Andrew-Sherwin/ECE395/Digital Target System/PCB Art/Asuka Langley/Asuka Langley w White Background.png

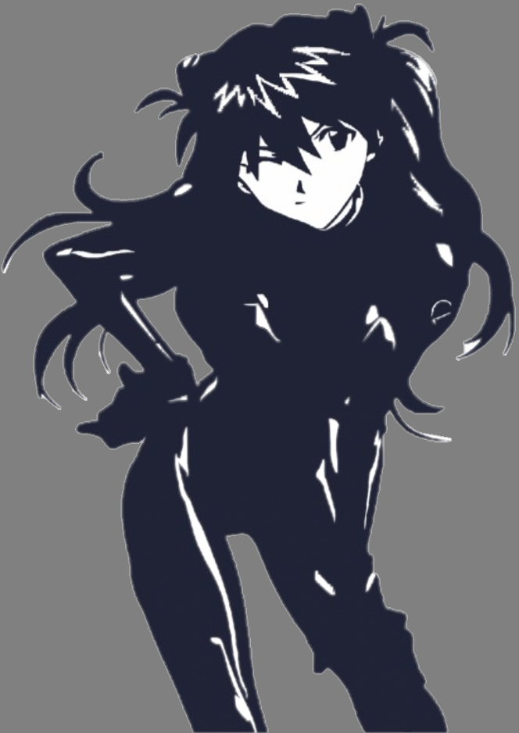
Digital Target System/PCB Art/Asuka Langley/Asuka Langley w White Background.png
