Andrew-Sherwin/ECE395/Digital Target System/PCB Art/Asuka Langley/Screen Shot 2023-11-08 at 3.01.39 AM.png

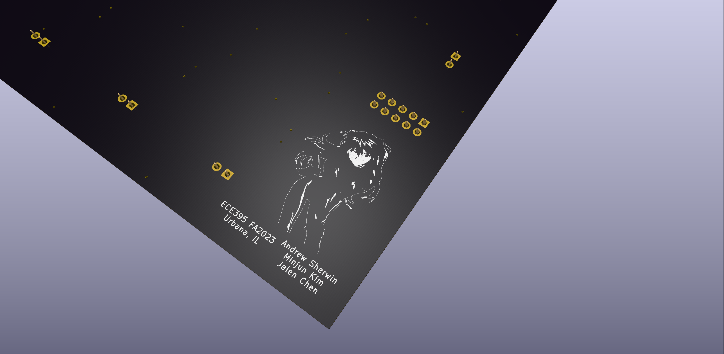
Digital Target System/PCB Art/Asuka Langley/Screen Shot 2023-11-08 at 3.01.39 AM.png
