Andrew-Sherwin/ECE395/Digital Target System/PCB Art/PSG Anime Girl/Screen Shot 2023-11-18 at 3.03.04 AM.png

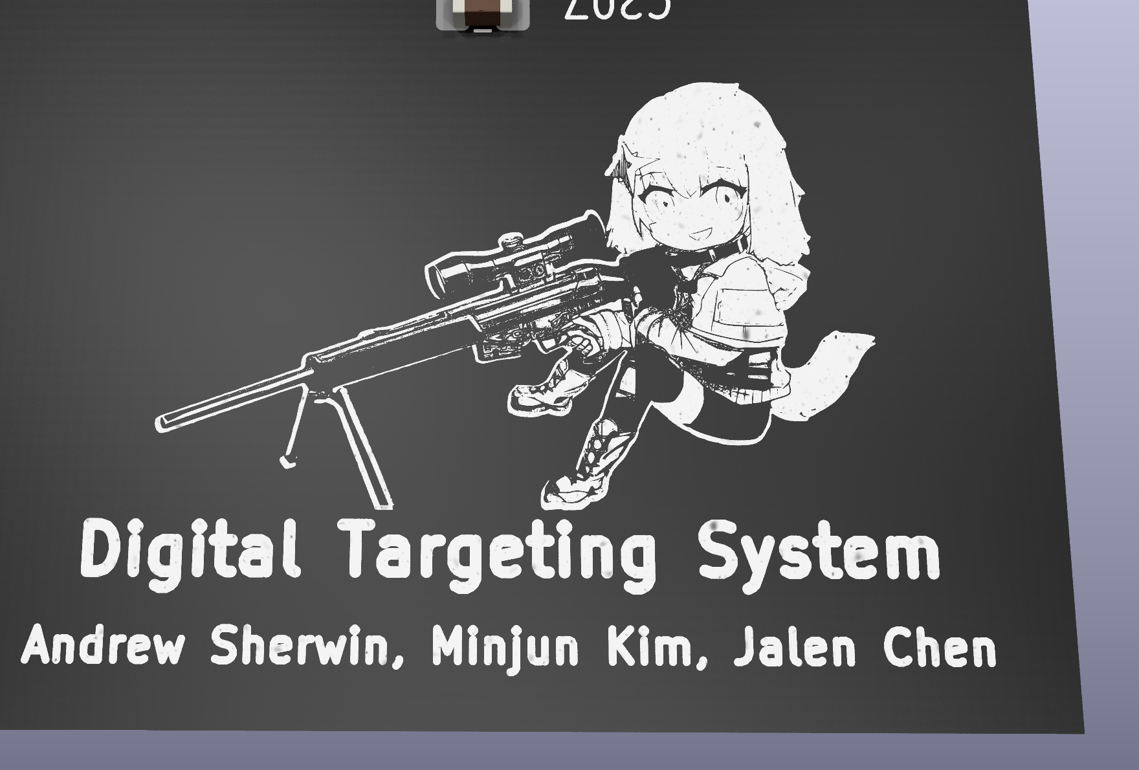
Digital Target System/PCB Art/PSG Anime Girl/Screen Shot 2023-11-18 at 3.03.04 AM.png
