Andrew-Sherwin/ECE395/Digital Target System/PCB Art/Mac Pro Backups w Art/Rev8/Misc Gerber/Gerber Files/ECE395_Digital_Target-F_Silkscreen.pdf

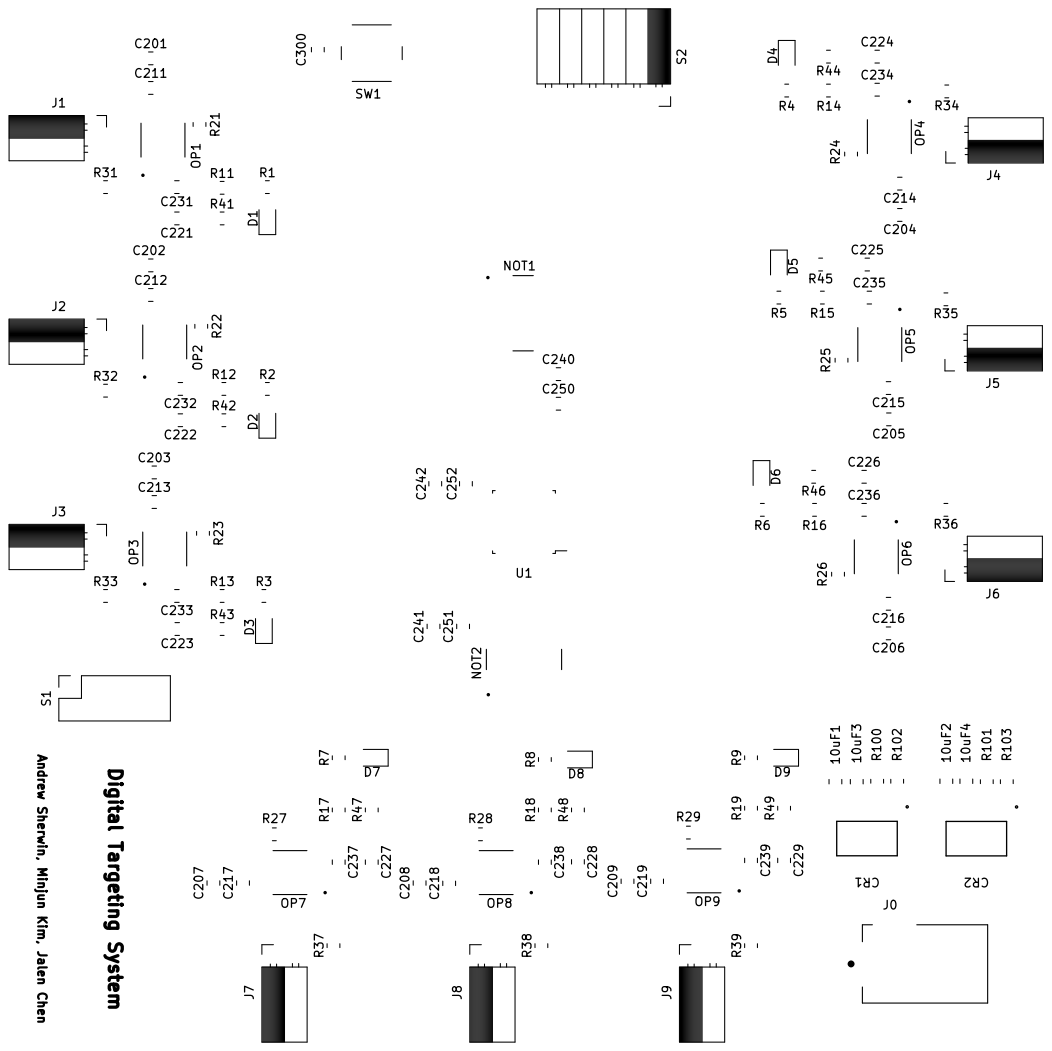
[picture p25: page 1]

Andrew Sherwin, Minjun Kim, Jalen Chen Digital Targeting System CR2 10uF3 C206 10uF4 S2 D6 C234 C232 OP9 OP4 OP6
